tylerhudd/theremin_glove/pcb/wiproc/wiproc/analog_cond.sch

## KiCad design pcb/wiproc/wiproc/analog_cond.sch (2019-10-28)

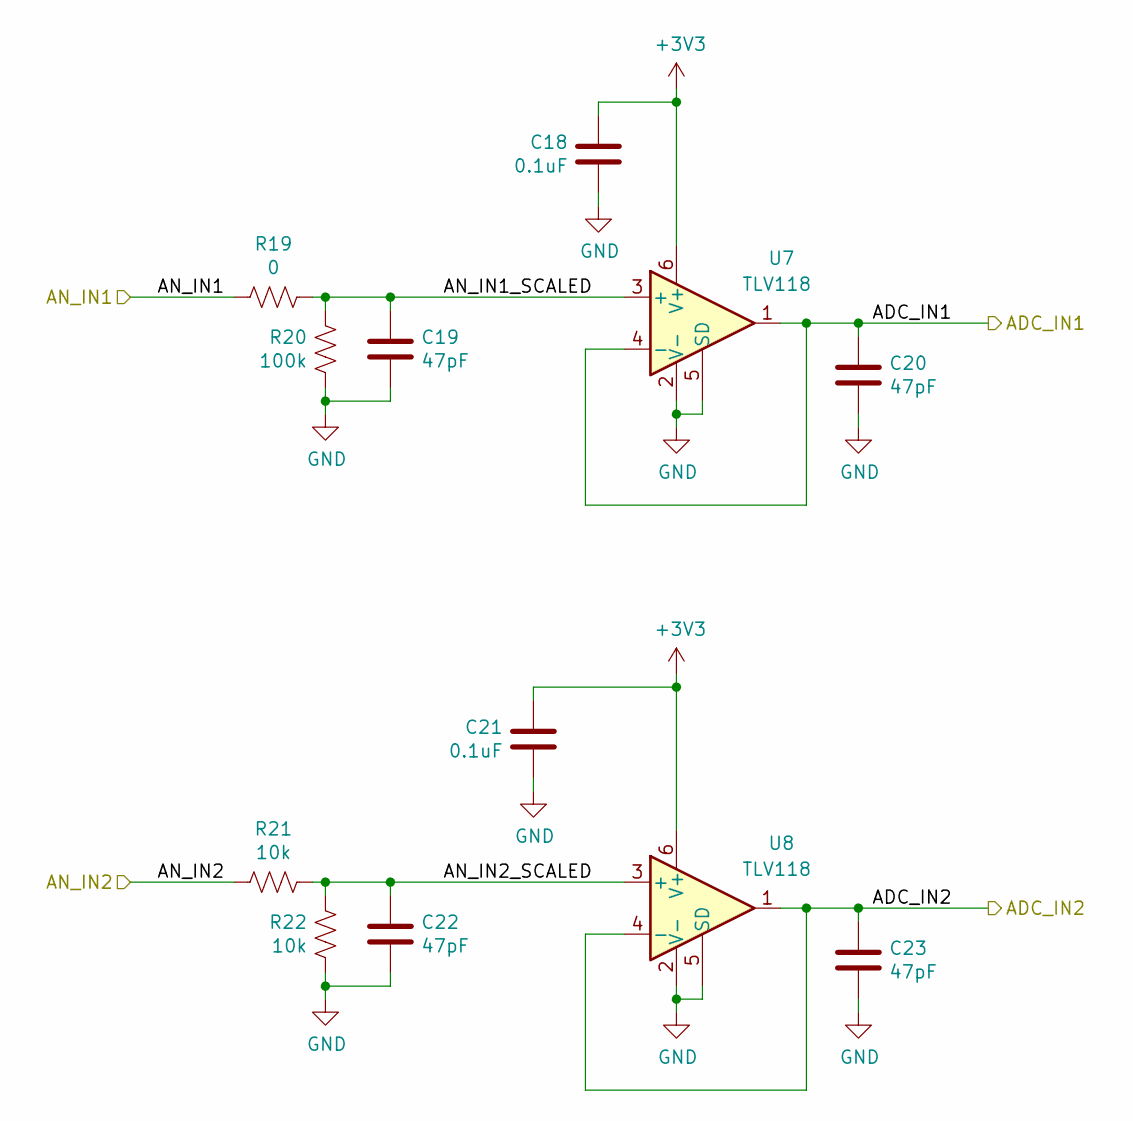
[picture p35: schematic analog_cond.sch]

Parts:
C18, C21: 0.1uF; C_0603_1608Metric_Pad1.05x0.95mm_HandSolder
C19, C20, C22, C23: 47pF; C_0603_1608Metric_Pad1.05x0.95mm_HandSolder
R19: 0; R_0603_1608Metric_Pad1.05x0.95mm_HandSolder
R20: 100k; R_0603_1608Metric_Pad1.05x0.95mm_HandSolder
R21, R22: 10k; R_0603_1608Metric_Pad1.05x0.95mm_HandSolder
U7, U8: TLV118; SOT-23-6

Connections:
+3V3: C18.1, C21.1, U7.6 (V+), U8.6 (V+)
ADC_IN1: C20.1, U7.1, U7.4 (-)
ADC_IN2: C23.1, U8.1, U8.4 (-)
AN_IN1: R19.1
AN_IN1_SCALED: C19.1, R19.2, R20.1, U7.3 (+)
AN_IN2: R21.1
AN_IN2_SCALED: C22.1, R21.2, R22.1, U8.3 (+)
GND: C18.2, C19.2, C20.2, C21.2, C22.2, C23.2, R20.2, R22.2, U7.2 (V-), U7.5 (SD), U8.2 (V-), U8.5 (SD)
