tylerhudd/theremin_glove/pcb/wiproc/wiproc/batt_chrg.sch

## KiCad design pcb/wiproc/wiproc/batt_chrg.sch (2019-10-28)

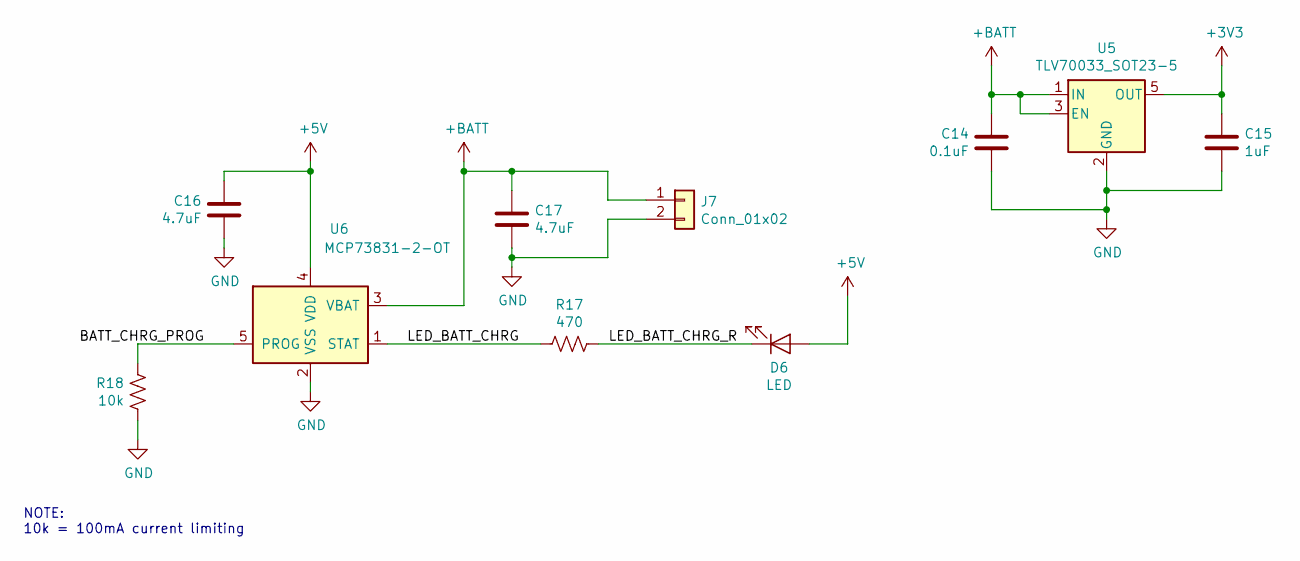
[picture p36: schematic batt_chrg.sch]

Parts:
C14: 0.1uF; C_0603_1608Metric_Pad1.05x0.95mm_HandSolder
C15: 1uF; C_0603_1608Metric_Pad1.05x0.95mm_HandSolder
C16, C17: 4.7uF; C_0603_1608Metric_Pad1.05x0.95mm_HandSolder
D6: LED; LED_0805_2012Metric_Pad1.15x1.40mm_HandSolder
J7: Conn_01x02; JST_PH_S2B-PH-SM4-TB_1x02-1MP_P2.00mm_Horizontal
R17: 470; R_0603_1608Metric_Pad1.05x0.95mm_HandSolder
R18: 10k; R_0603_1608Metric_Pad1.05x0.95mm_HandSolder
U5: TLV70033_SOT23-5; SOT-23-5
U6: MCP73831-2-OT; SOT-23-5

Connections:
+3V3: C15.1, U5.5 (OUT)
+5V: C16.1, D6.2 (A), U6.4 (VDD)
+BATT: C14.1, C17.1, J7.1, U5.1 (IN), U5.3 (EN), U6.3 (VBAT)
BATT_CHRG_PROG: R18.1, U6.5 (PROG)
GND: C14.2, C15.2, C16.2, C17.2, J7.2, R18.2, U5.2 (GND), U6.2 (VSS)
LED_BATT_CHRG: R17.2, U6.1 (STAT)
LED_BATT_CHRG_R: D6.1 (K), R17.1

Notes on the sheet:
NOTE: 10k = 100mA current limiting
