tylerhudd/theremin_glove/pcb/wiproc/wiproc/mcu_atmega328p.sch

## KiCad design pcb/wiproc/wiproc/mcu_atmega328p.sch (2019-10-28)

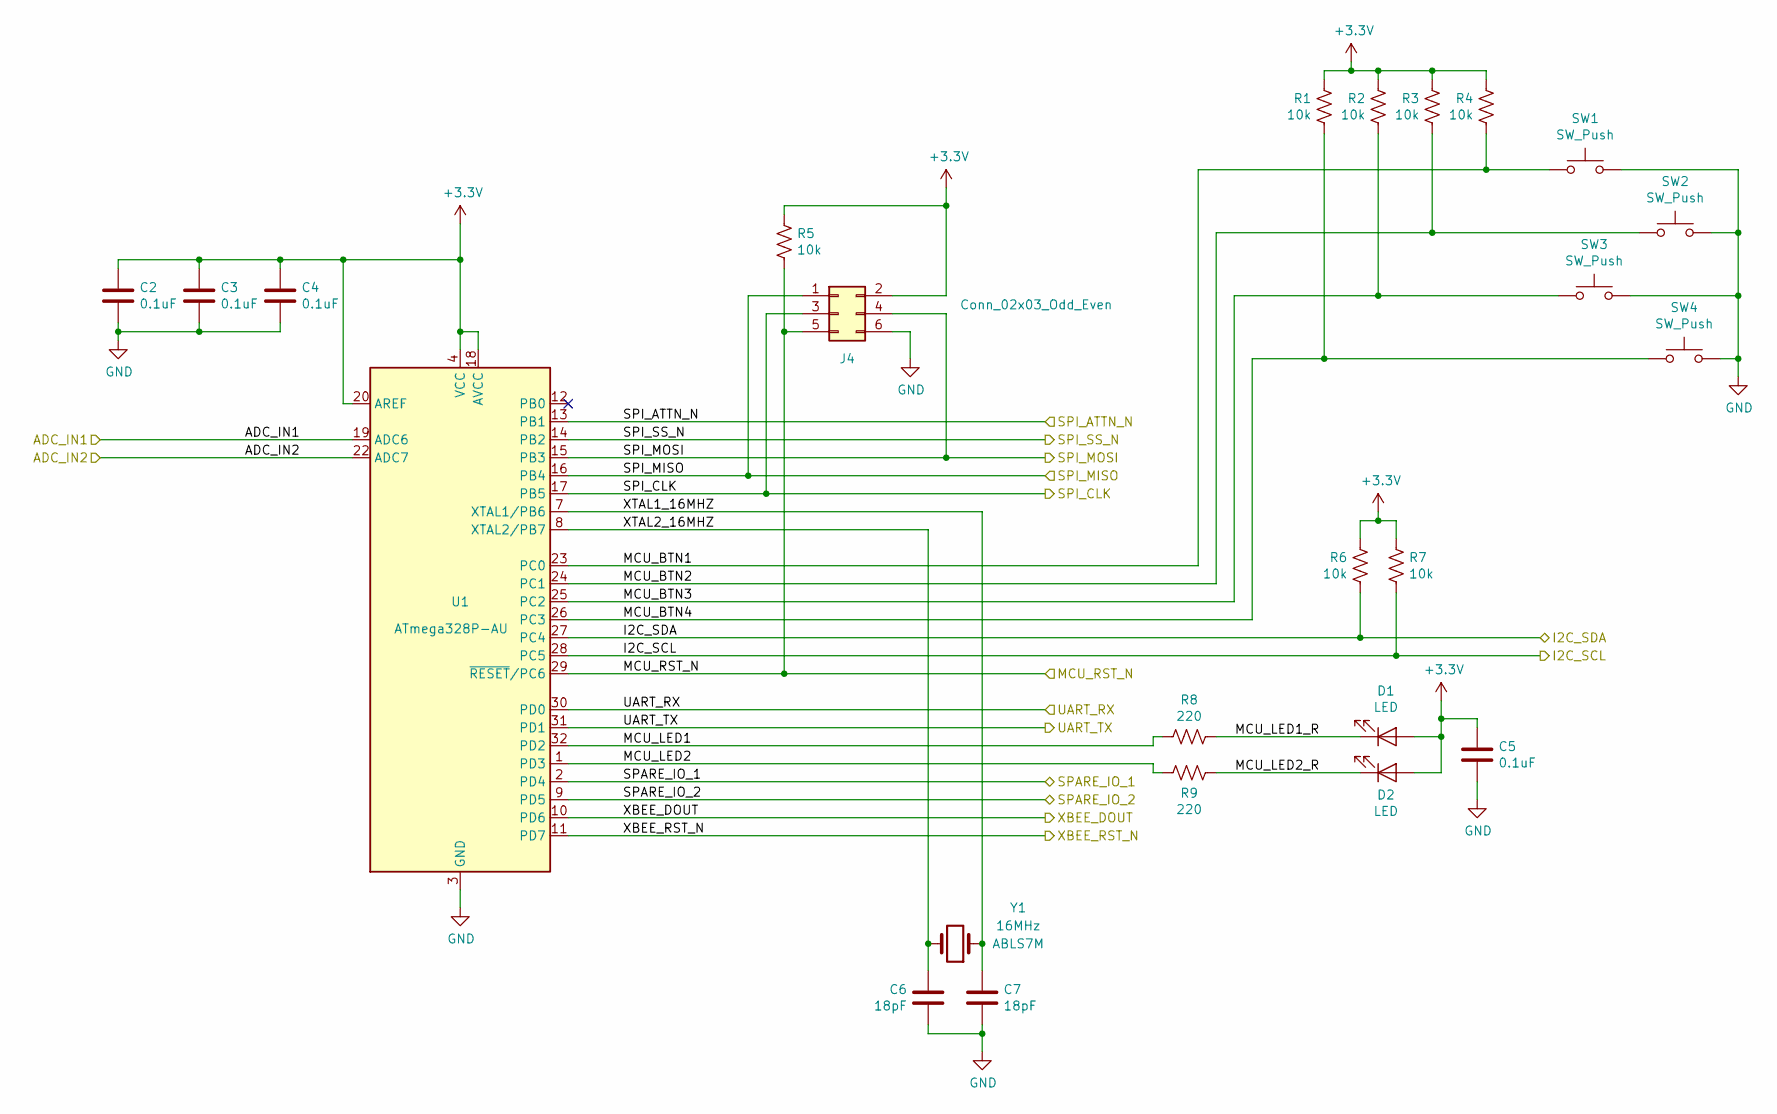
[picture p37: schematic mcu_atmega328p.sch]

Parts:
C2, C3, C4, C5: 0.1uF; C_0603_1608Metric_Pad1.05x0.95mm_HandSolder
C6, C7: 18pF; C_0603_1608Metric_Pad1.05x0.95mm_HandSolder
D1, D2: LED; LED_0805_2012Metric_Pad1.15x1.40mm_HandSolder
J4: Conn_02x03_Odd_Even; PinHeader_2x03_P2.54mm_Vertical_SMD
R1, R2, R3, R4, R5, R6, R7: 10k; R_0603_1608Metric_Pad1.05x0.95mm_HandSolder
R8, R9: 220; R_0603_1608Metric_Pad1.05x0.95mm_HandSolder
SW1, SW2, SW3, SW4: SW_Push; SW_SPST_TL3342
U1: ATmega328P-AU; TQFP-32_7x7mm_P0.8mm
Y1: 16MHz; Crystal_SMD_ECS_CSM3X-2Pin_7.6x4.1mm

Connections:
+3.3V: C2.1, C3.1, C4.1, C5.1, D1.2 (A), D2.2 (A), J4.2, R1.1, R2.1, R3.1, R4.1, R5.1, R6.1, R7.1, U1.4 (VCC), U1.6 (VCC), U1.18 (AVCC), U1.20 (AREF)
ADC_IN1: U1.19 (ADC6)
ADC_IN2: U1.22 (ADC7)
GND: C2.2, C3.2, C4.2, C5.2, C6.2, C7.2, J4.6, SW1.2, SW2.2, SW3.2, SW4.2, U1.3 (GND), U1.5 (GND), U1.21 (GND)
I2C_SCL: R7.2, U1.28 (PC5)
I2C_SDA: R6.2, U1.27 (PC4)
MCU_BTN1: R4.2, SW1.1, U1.23 (PC0)
MCU_BTN2: R3.2, SW2.1, U1.24 (PC1)
MCU_BTN3: R2.2, SW3.1, U1.25 (PC2)
MCU_BTN4: R1.2, SW4.1, U1.26 (PC3)
MCU_LED1: R8.2, U1.32 (PD2)
MCU_LED1_R: D1.1 (K), R8.1
MCU_LED2: R9.2, U1.1 (PD3)
MCU_LED2_R: D2.1 (K), R9.1
MCU_RST_N: J4.5, R5.2, U1.29 (~RESET~/PC6)
SPARE_IO_1: U1.2 (PD4)
SPARE_IO_2: U1.9 (PD5)
SPI_ATTN_N: U1.13 (PB1)
SPI_CLK: J4.3, U1.17 (PB5)
SPI_MISO: J4.1, U1.16 (PB4)
SPI_MOSI: J4.4, U1.15 (PB3)
SPI_SS_N: U1.14 (PB2)
UART_RX: U1.30 (PD0)
UART_TX: U1.31 (PD1)
XBEE_DOUT: U1.10 (PD6)
XBEE_RST_N: U1.11 (PD7)
XTAL1_16MHZ: C7.1, U1.7 (XTAL1/PB6), Y1.1
XTAL2_16MHZ: C6.1, U1.8 (XTAL2/PB7), Y1.2
