tylerhudd/theremin_glove/pcb/wiproc/wiproc/usb_uart.sch

## KiCad design pcb/wiproc/wiproc/usb_uart.sch (2019-10-28)

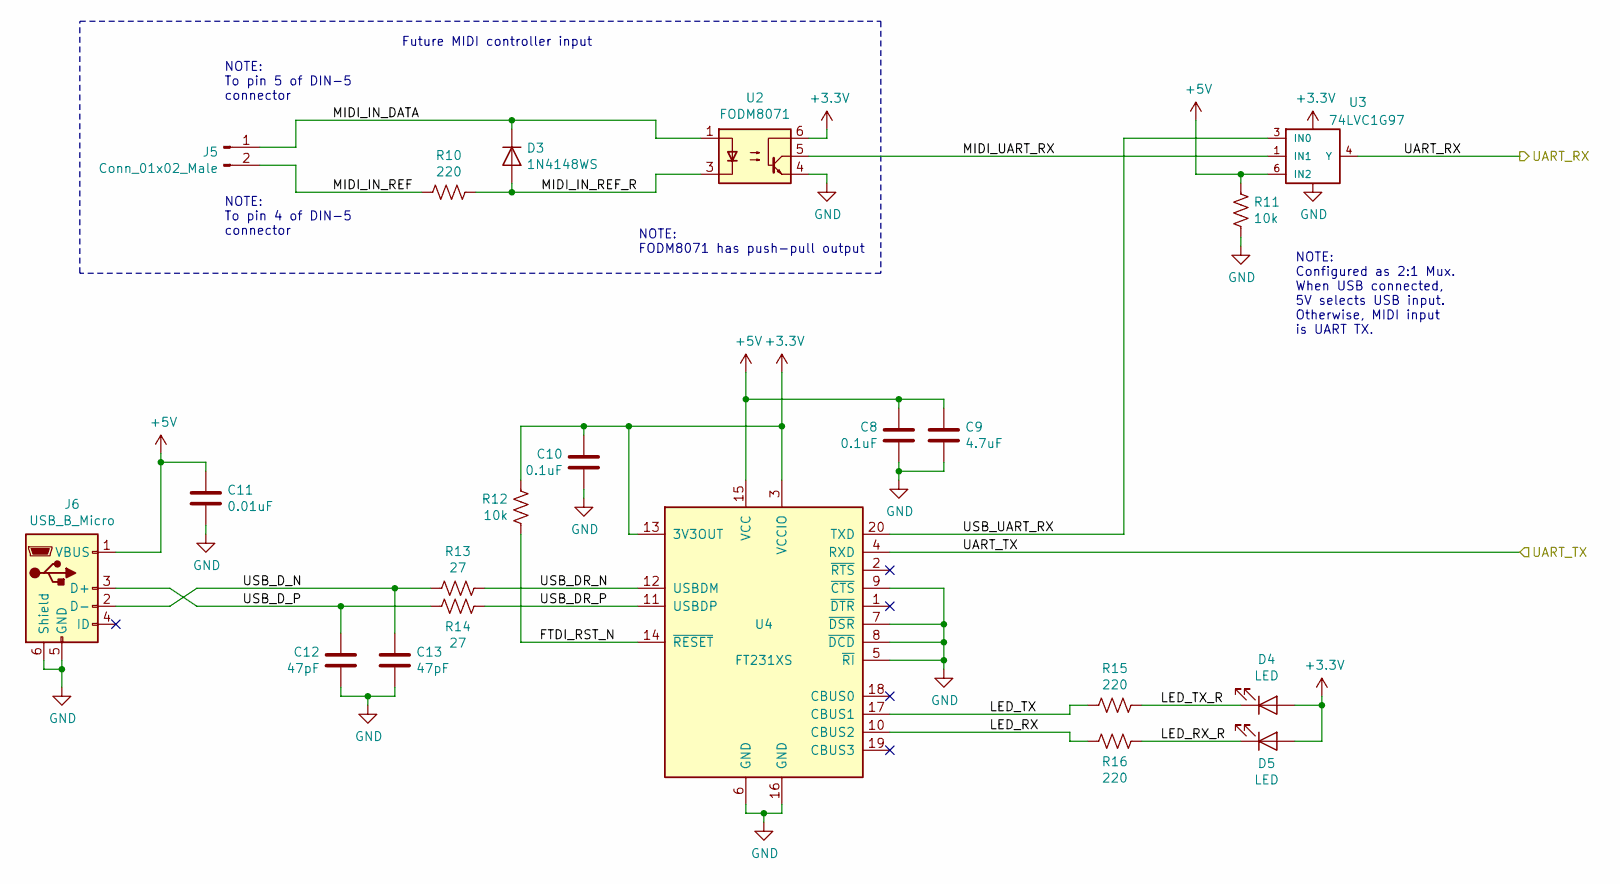
[picture p38: schematic usb_uart.sch]

Parts:
C8, C10: 0.1uF; C_0603_1608Metric_Pad1.05x0.95mm_HandSolder
C9: 4.7uF; C_0603_1608Metric_Pad1.05x0.95mm_HandSolder
C11: 0.01uF; C_0603_1608Metric_Pad1.05x0.95mm_HandSolder
C12, C13: 47pF; C_0603_1608Metric_Pad1.05x0.95mm_HandSolder
D3: 1N4148WS; D_SOD-323_HandSoldering
D4, D5: LED; LED_0805_2012Metric_Pad1.15x1.40mm_HandSolder
J5: Conn_01x02_Male; PinHeader_1x02_P2.54mm_Vertical
J6: USB_B_Micro; USB_Micro-B_Molex_47346-0001
R10, R15, R16: 220; R_0603_1608Metric_Pad1.05x0.95mm_HandSolder
R11, R12: 10k; R_0603_1608Metric_Pad1.05x0.95mm_HandSolder
R13, R14: 27; R_0603_1608Metric_Pad1.05x0.95mm_HandSolder
U2: FODM8071; SO-5_4.4x3.6mm_P1.27mm
U3: 74LVC1G97; SOT-23-6
U4: FT231XS; SSOP-20_3.9x8.7mm_P0.635mm

Connections:
+3.3V: C10.1, D4.2 (A), D5.2 (A), R12.1, U2.6, U3.5 (VCC), U4.3 (VCCIO), U4.13 (3V3OUT)
+5V: C8.1, C9.1, C11.1, J6.1 (VBUS), R11.1, U3.6 (IN2), U4.15 (VCC)
FTDI_RST_N: R12.2, U4.14 (~RESET)
GND: C8.2, C9.2, C10.2, C11.2, C12.2, C13.2, J6.5 (GND), J6.6 (Shield), R11.2, U2.4, U3.2 (GND), U4.5 (~RI), U4.6 (GND), U4.7 (~DSR), U4.8 (~DCD), U4.9 (~CTS), U4.16 (GND)
LED_RX: R16.2, U4.10 (CBUS2)
LED_RX_R: D5.1 (K), R16.1
LED_TX: R15.2, U4.17 (CBUS1)
LED_TX_R: D4.1 (K), R15.1
MIDI_IN_DATA: D3.1 (K), J5.1, U2.1
MIDI_IN_REF: J5.2, R10.2
MIDI_IN_REF_R: D3.2 (A), R10.1, U2.3
MIDI_UART_RX: U2.5, U3.1 (IN1)
UART_RX: U3.4 (Y)
UART_TX: U4.4 (RXD)
USB_DR_N: R13.1, U4.12 (USBDM)
USB_DR_P: R14.1, U4.11 (USBDP)
USB_D_N: C13.1, J6.2 (D-), R13.2
USB_D_P: C12.1, J6.3 (D+), R14.2
USB_UART_RX: U3.3 (IN0), U4.20 (TXD)

Notes on the sheet:
NOTE: FODM8071 has push-pull output
NOTE: To pin 4 of DIN-5 connector
NOTE: To pin 5 of DIN-5 connector
Future MIDI controller input
NOTE: Configured as 2:1 Mux. When USB connected, 5V selects USB input. Otherwise, MIDI input is UART TX.
