tylerhudd/theremin_glove/pcb/wiproc/wiproc/wiproc.sch

## KiCad design pcb/wiproc/wiproc/wiproc.sch (2019-10-28)

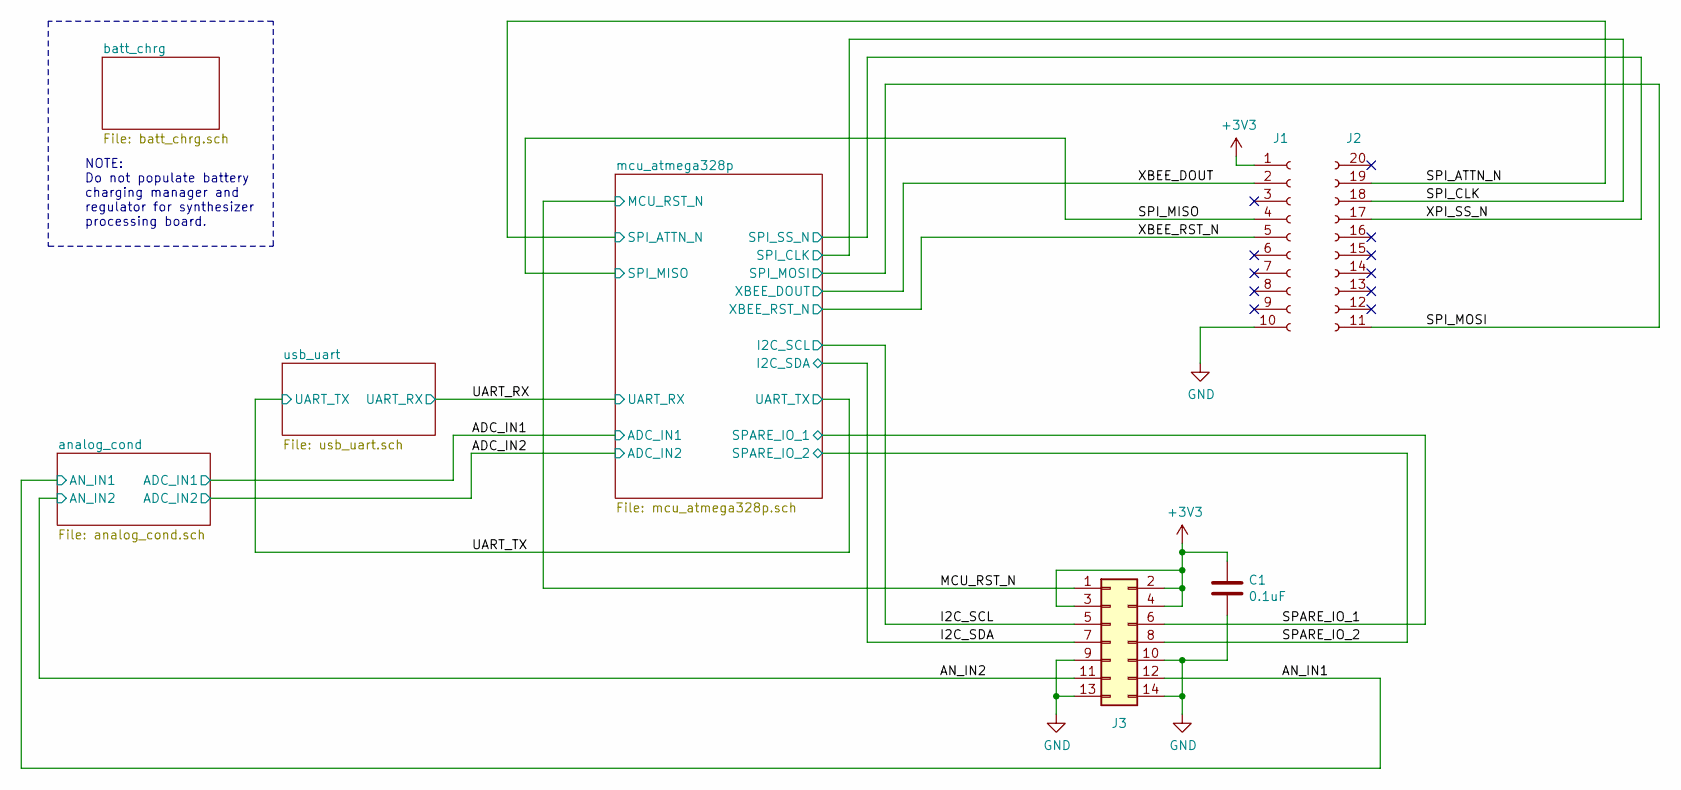
[picture p39: schematic wiproc.sch]

Parts:
C1: 0.1uF; C_0603_1608Metric_Pad1.05x0.95mm_HandSolder
J1: Conn_01x10_Female; PinSocket_1x10_P2.00mm_Vertical
J2: Conn_01x10_Female_xbee; PinSocket_1x10_P2.00mm_Vertical
J3: Conn_02x07_Odd_Even; PinHeader_2x07_P2.54mm_Vertical

Connections:
+3V3: C1.1, J1.1, J3.2, J3.3, J3.4
AN_IN1: J3.12
AN_IN2: J3.11
GND: C1.2, J1.10, J3.9, J3.10, J3.13, J3.14
I2C_SCL: J3.5
I2C_SDA: J3.7
MCU_RST_N: J3.1
SPARE_IO_1: J3.6
SPARE_IO_2: J3.8
SPI_ATTN_N: J2.19 (Pin_2)
SPI_CLK: J2.18 (Pin_3)
SPI_MISO: J1.4
SPI_MOSI: J2.11 (Pin_10)
XBEE_DOUT: J1.2
XBEE_RST_N: J1.5
XPI_SS_N: J2.17 (Pin_4)

Notes on the sheet:
NOTE: Do not populate battery charging manager and regulator for synthesizer processing board.
